ifilot/sap-smd/img/arithmetic_and_logic_unit_rev1.png

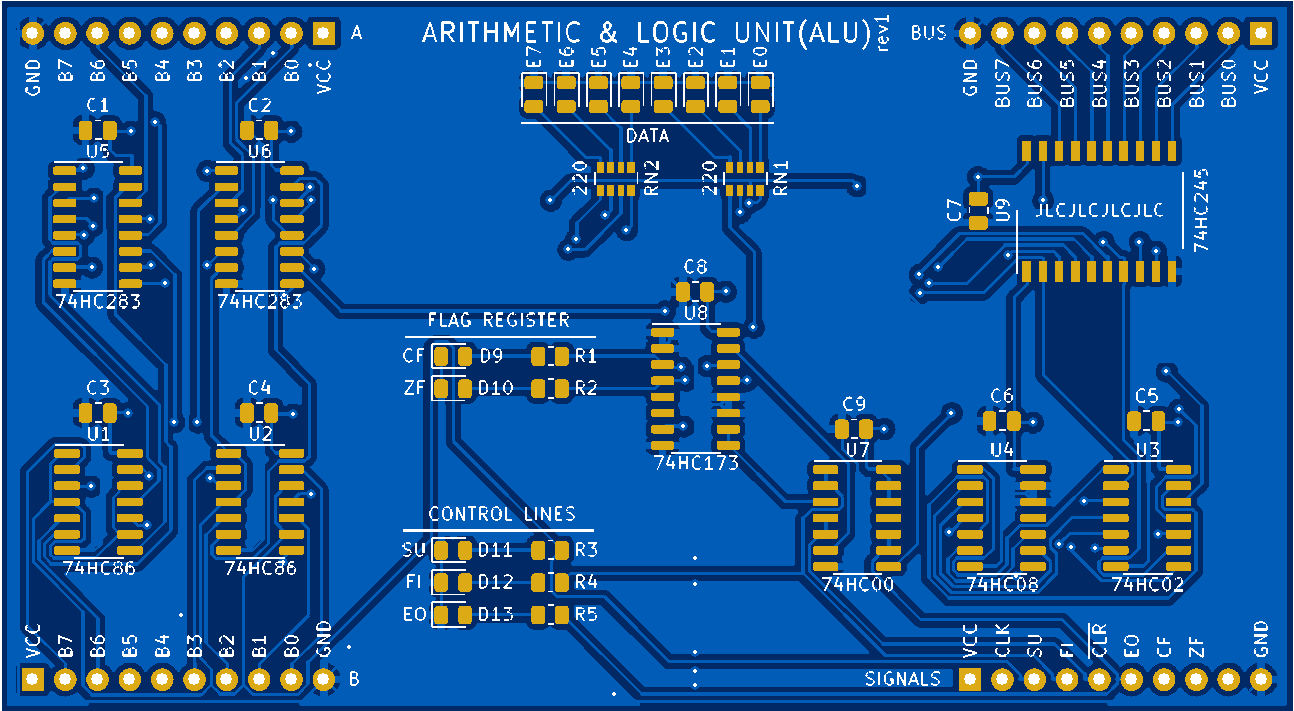
img/arithmetic_and_logic_unit_rev1.png
