ifilot/sap-smd/img/instruction_decoder.png

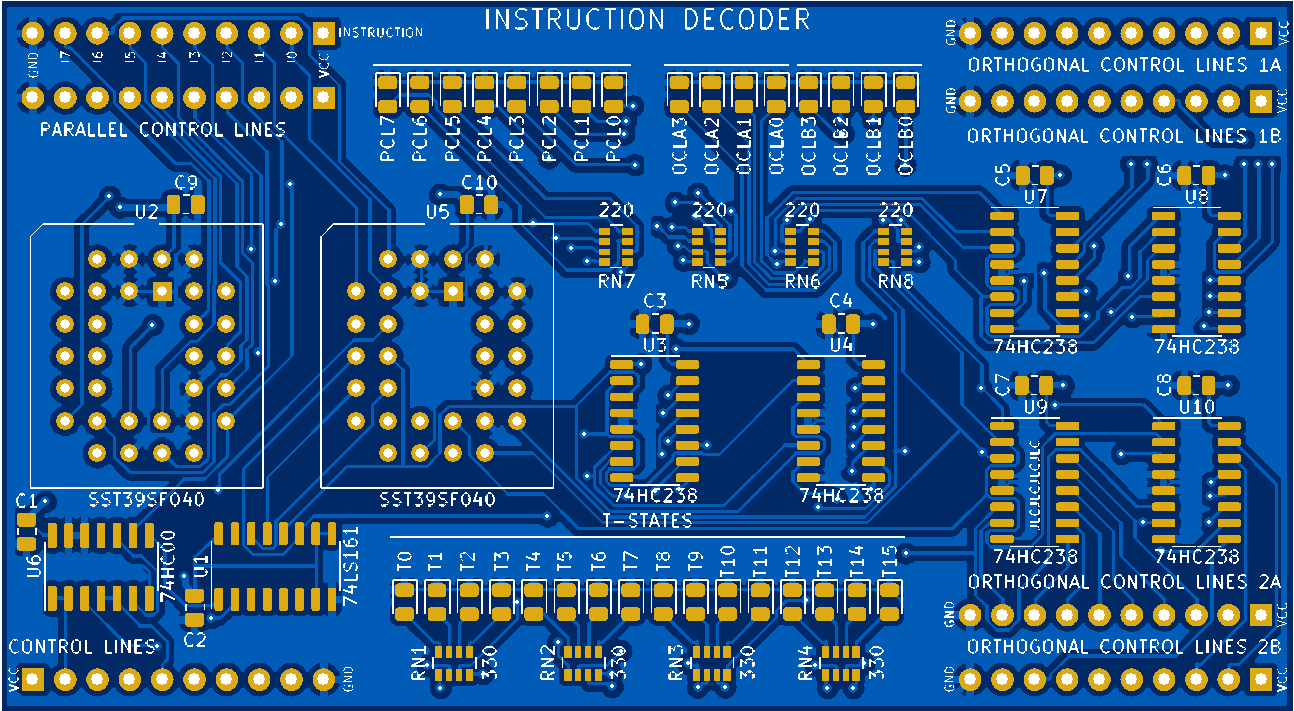
img/instruction_decoder.png
